bog739/gps_gsm_prj/RP2040_SW/url_format.py

class URL:
    url_google_maps = 'https://www.google.com/maps/@#,$,14z'
    url_google_maps_satellite = "http://www.google.com/maps/place/#,$/@#,$,19z/data=!3m1!1e3"
    url_google_maps_normal = "http://www.google.com/maps/place/#,/@#,$,19z/data=!3m1!4b1"
    flg_url_state = False
    
    
    
